chirauki/open-rally-remote/docs/images/complete-remote-v0.17-iso.png

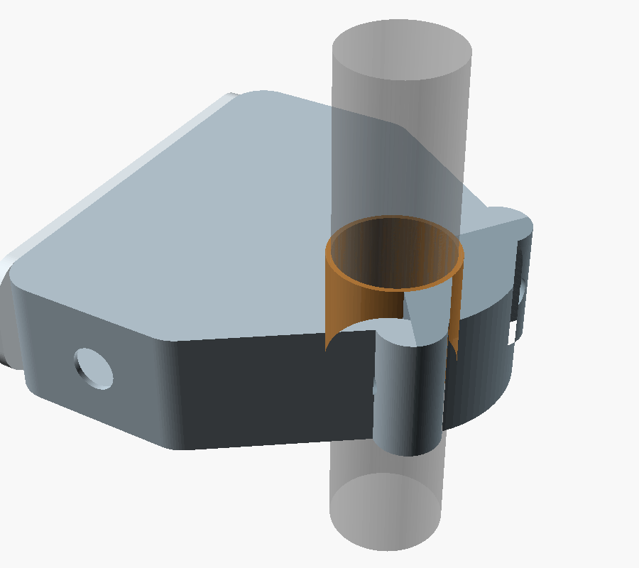
docs/images/complete-remote-v0.17-iso.png
