chirauki/open-rally-remote/docs/images/complete-remote-v0.17-top.png

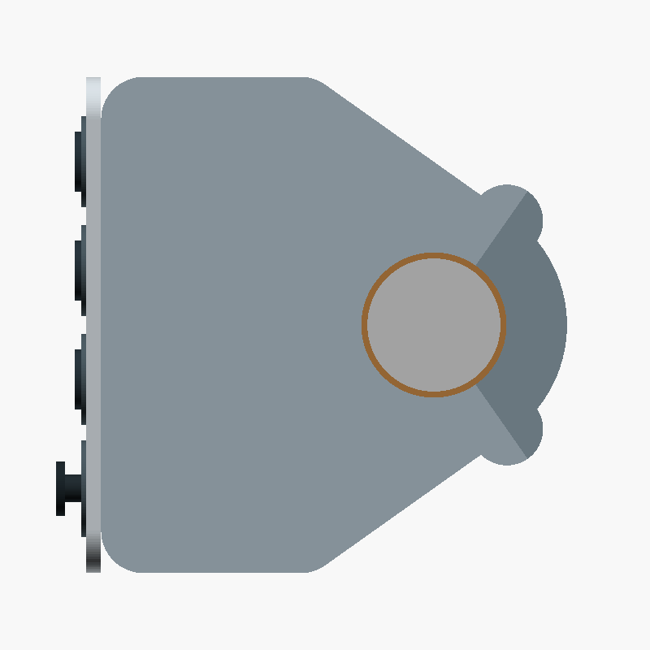
docs/images/complete-remote-v0.17-top.png
