chirauki/open-rally-remote/docs/images/complete-remote-v0.18-iso.png

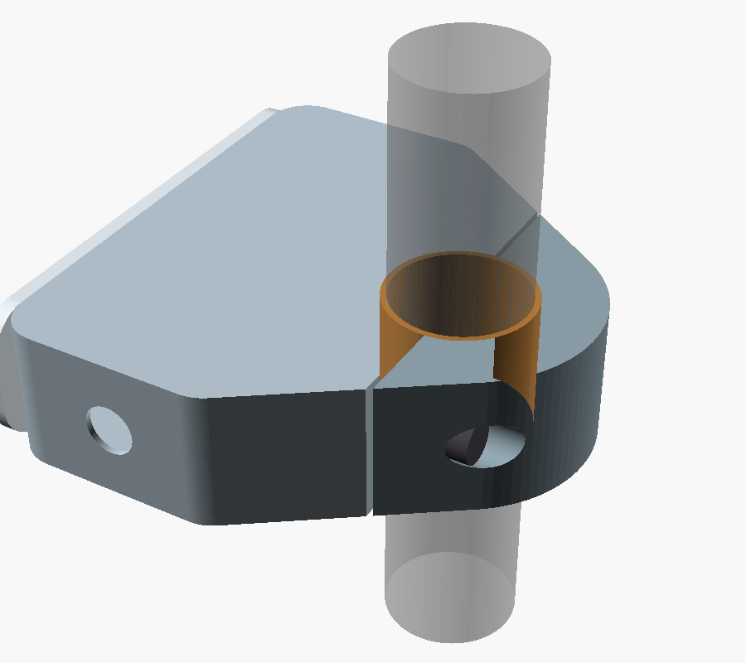
docs/images/complete-remote-v0.18-iso.png
