chirauki/open-rally-remote/docs/images/complete-remote-v0.18-rear.png

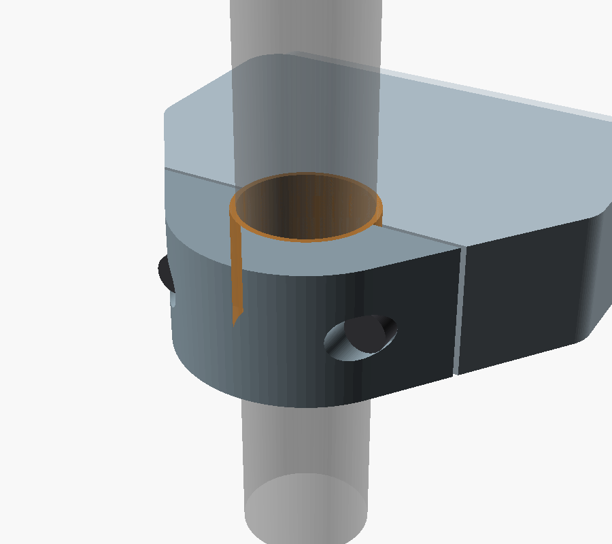
docs/images/complete-remote-v0.18-rear.png
