chirauki/open-rally-remote/docs/images/complete-remote-v0.18-section.png

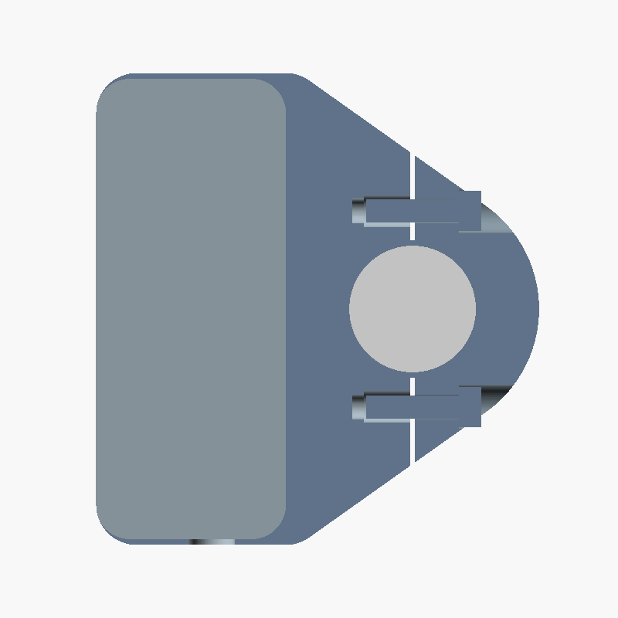
docs/images/complete-remote-v0.18-section.png
