chirauki/open-rally-remote/docs/images/complete-remote-v0.19-front.png

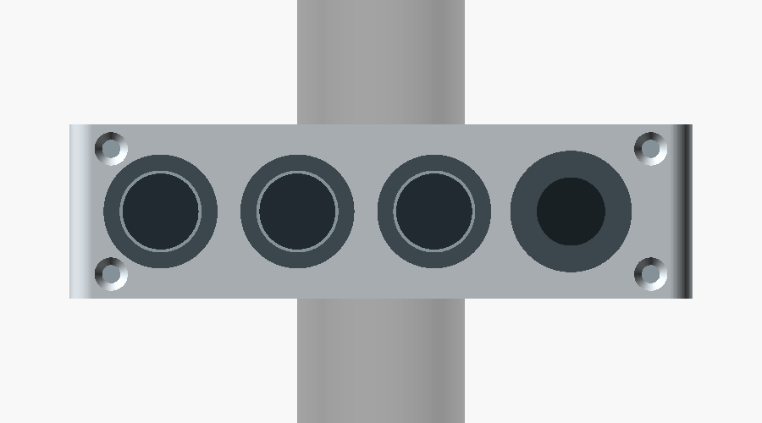
docs/images/complete-remote-v0.19-front.png
