chirauki/open-rally-remote/docs/images/complete-remote-v0.19-interior.png

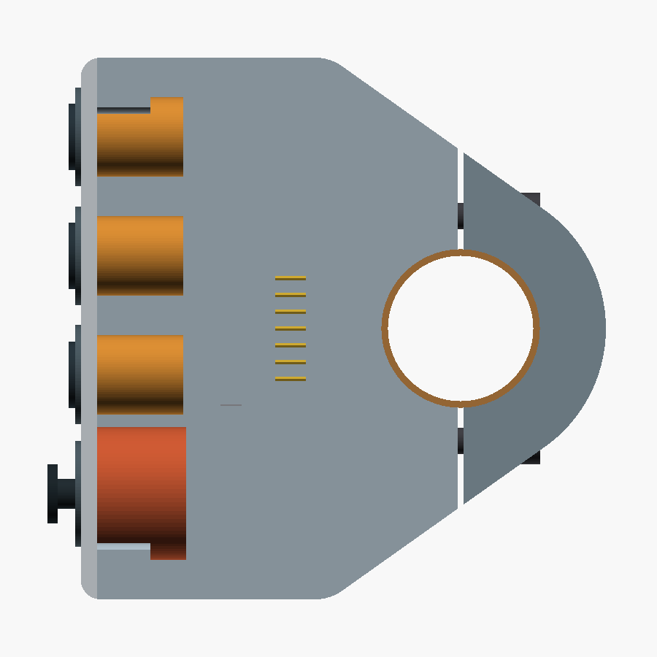
docs/images/complete-remote-v0.19-interior.png
