chirauki/open-rally-remote/docs/images/complete-remote-v0.20-front.png

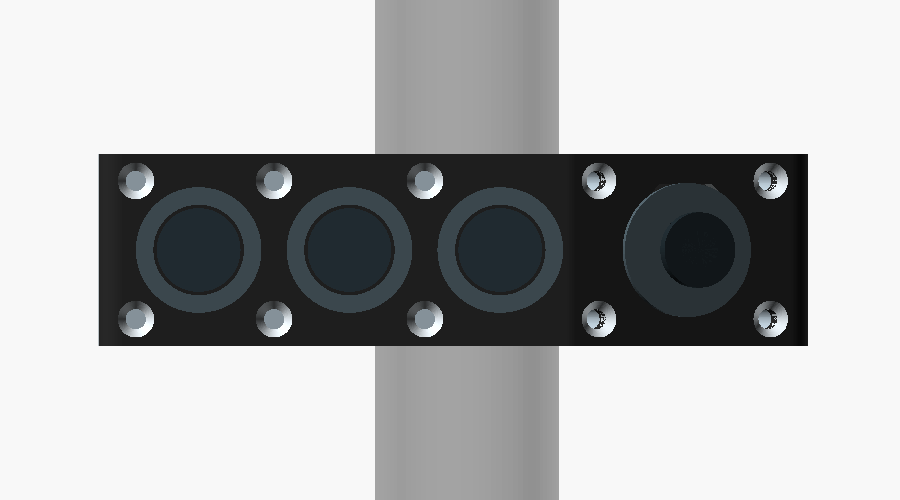
docs/images/complete-remote-v0.20-front.png
