chirauki/open-rally-remote/docs/images/complete-remote-v0.20-gasket-flat.png

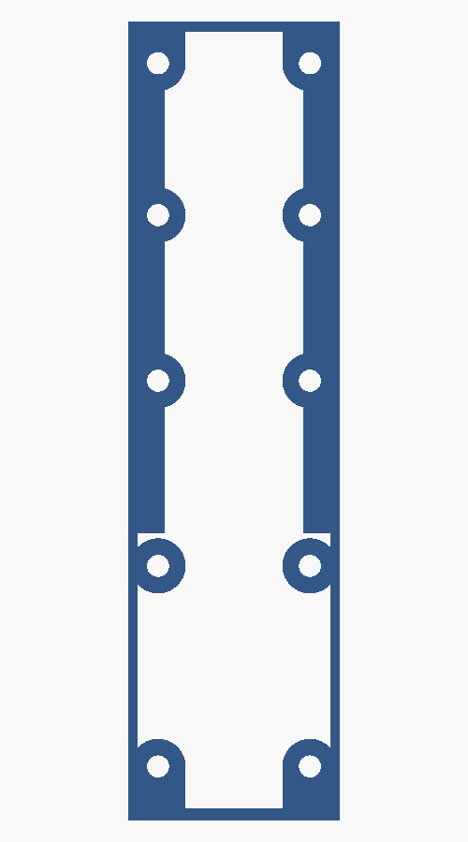
docs/images/complete-remote-v0.20-gasket-flat.png
