chirauki/open-rally-remote/docs/images/complete-remote-v0.20-interior-iso.png

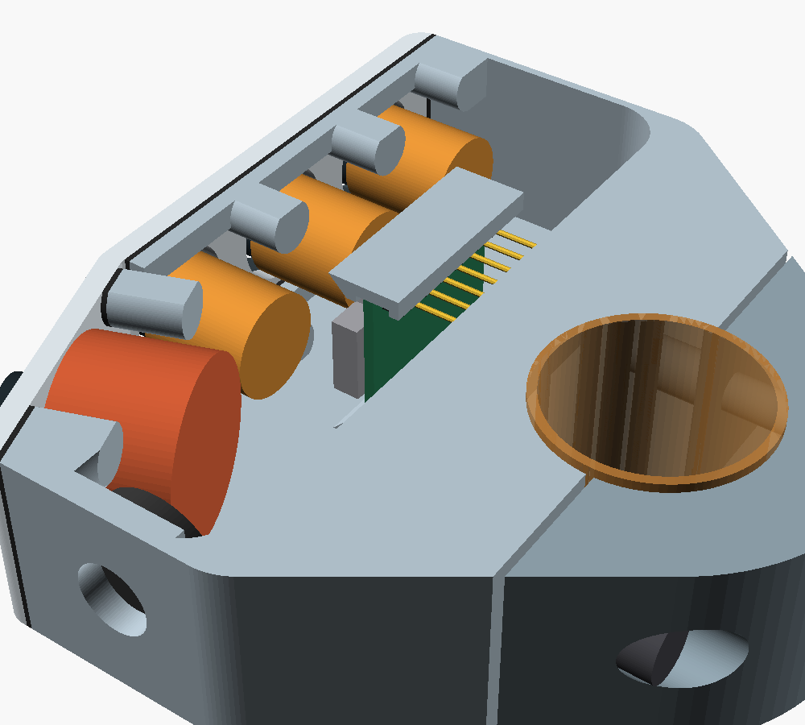
docs/images/complete-remote-v0.20-interior-iso.png
