chirauki/open-rally-remote/docs/images/complete-remote-v0.20-side.png

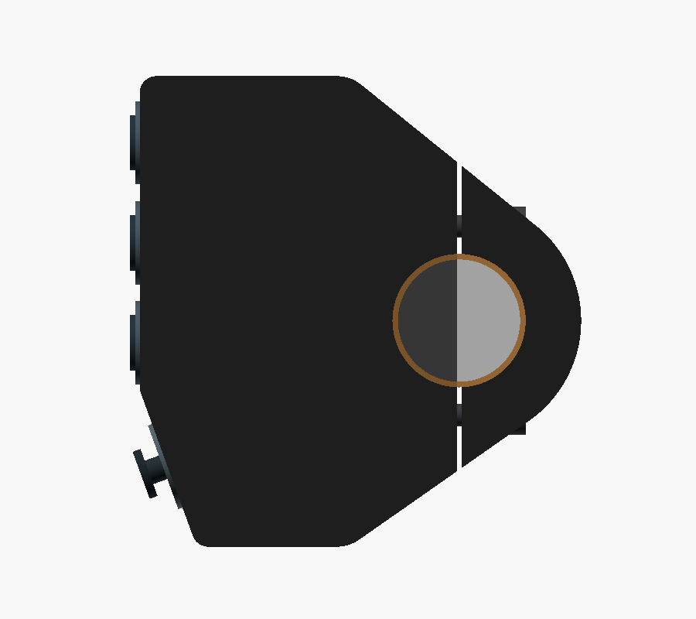
docs/images/complete-remote-v0.20-side.png
