chirauki/open-rally-remote/docs/images/complete-remote-v0.21-gasket-flat.png

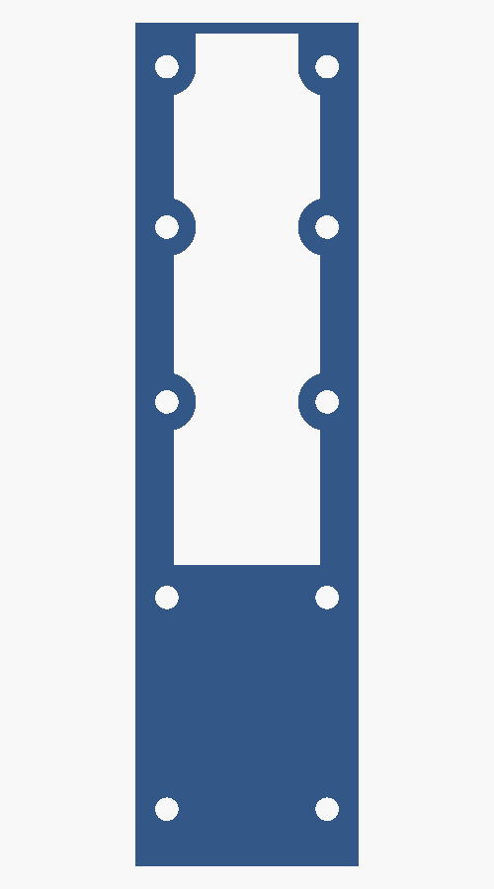
docs/images/complete-remote-v0.21-gasket-flat.png
