chirauki/open-rally-remote/docs/images/complete-remote-v0.21-interior-iso.png

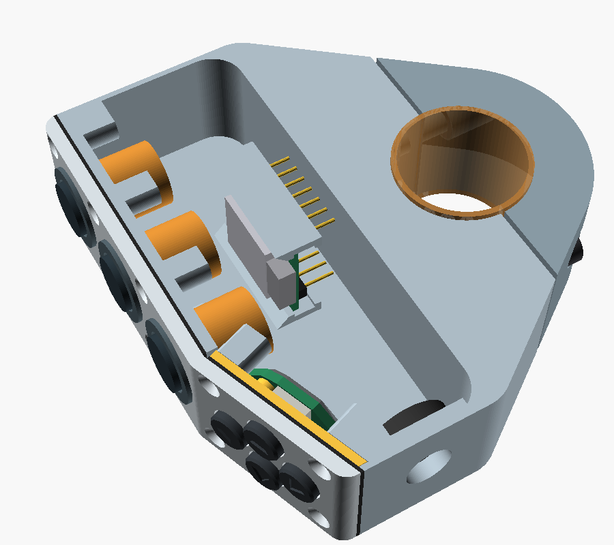
docs/images/complete-remote-v0.21-interior-iso.png
