chirauki/open-rally-remote/docs/images/complete-remote-v0.21-pad.png

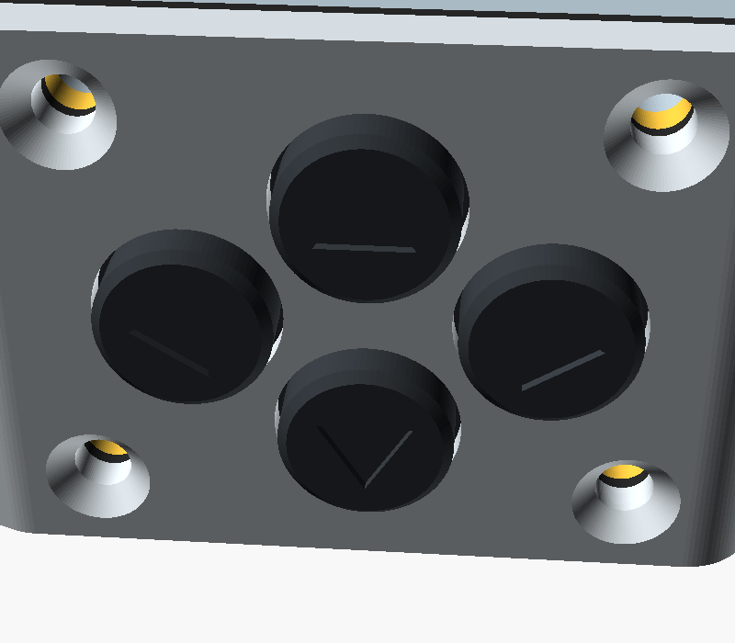
docs/images/complete-remote-v0.21-pad.png
