chirauki/open-rally-remote/docs/images/complete-remote-v0.22-joy-section.png

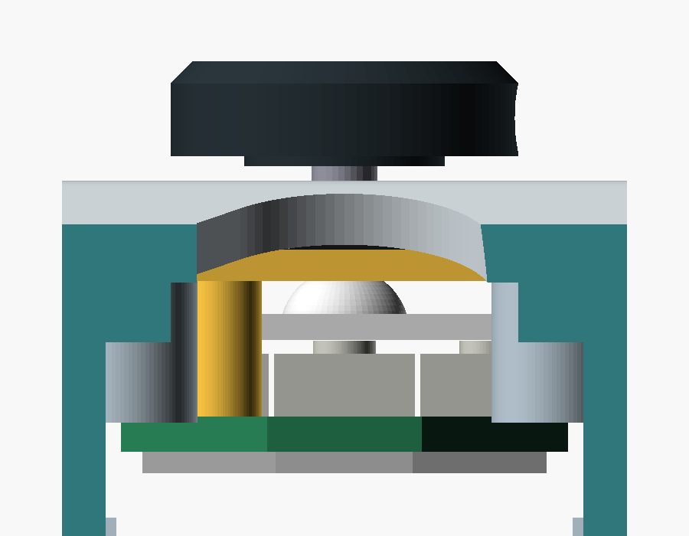
docs/images/complete-remote-v0.22-joy-section.png
